blinken/power-rail-probe/doc/1.jpg

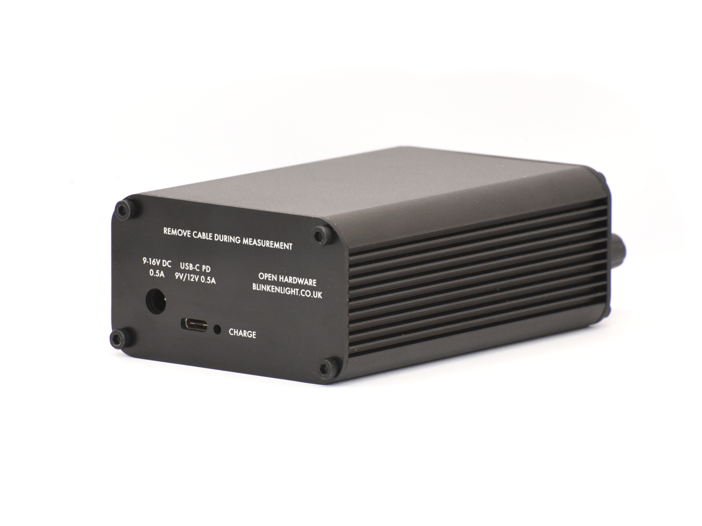
doc/1.jpg
