blinken/power-rail-probe/doc/2.jpg

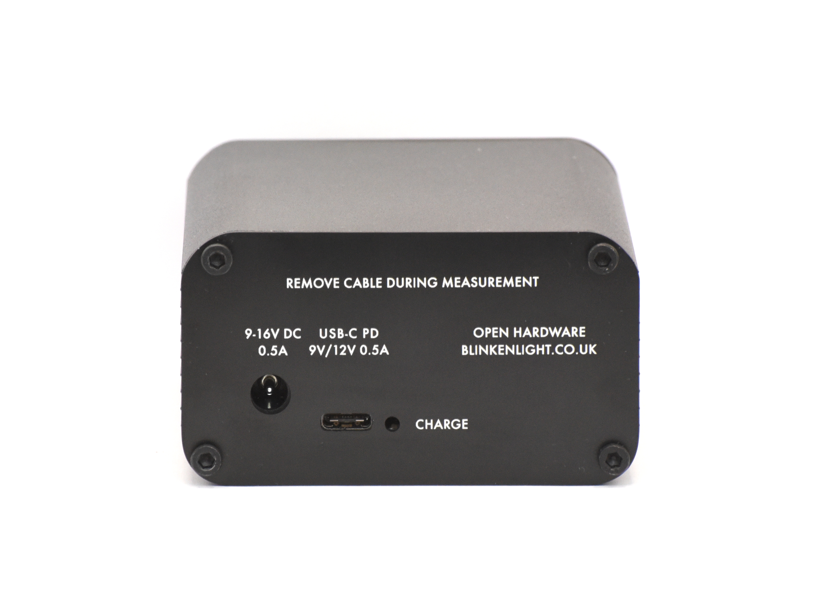
doc/2.jpg
