blinken/power-rail-probe/doc/3.jpg

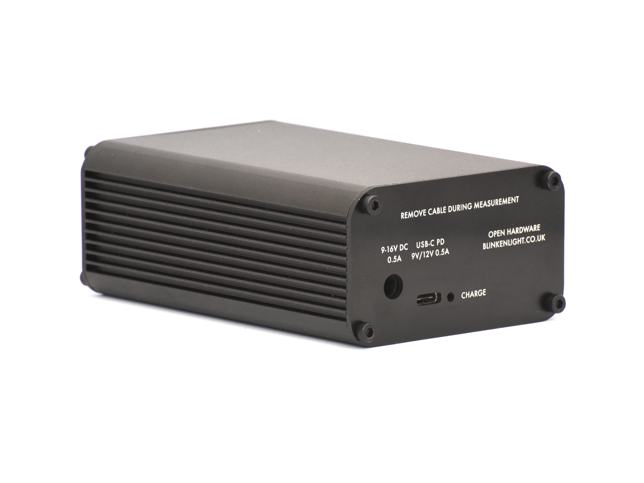
doc/3.jpg
