blinken/power-rail-probe/doc/4-crop.jpg

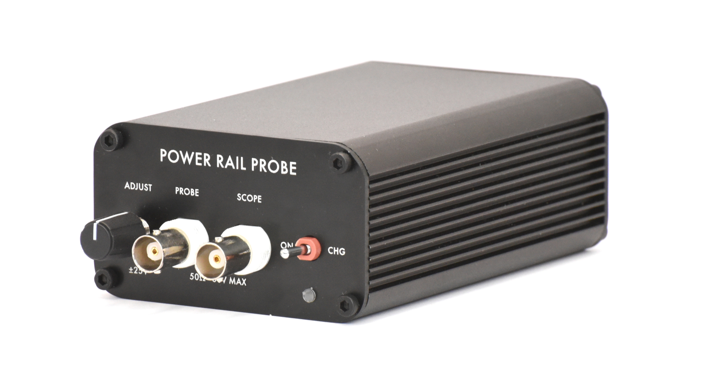
doc/4-crop.jpg
