blinken/power-rail-probe/doc/4.jpg

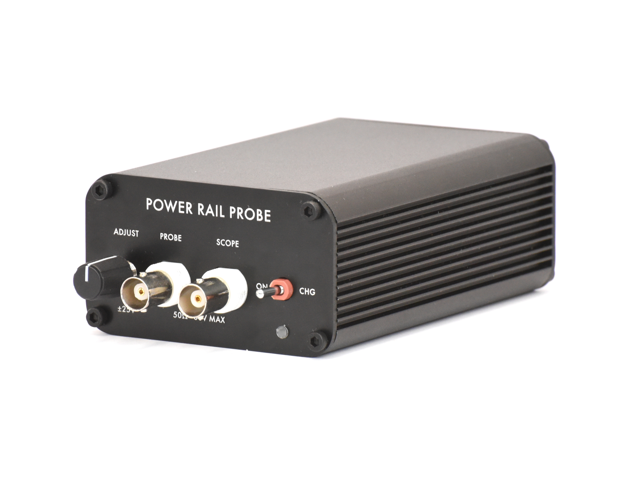
doc/4.jpg
