blinken/power-rail-probe/doc/5.jpg

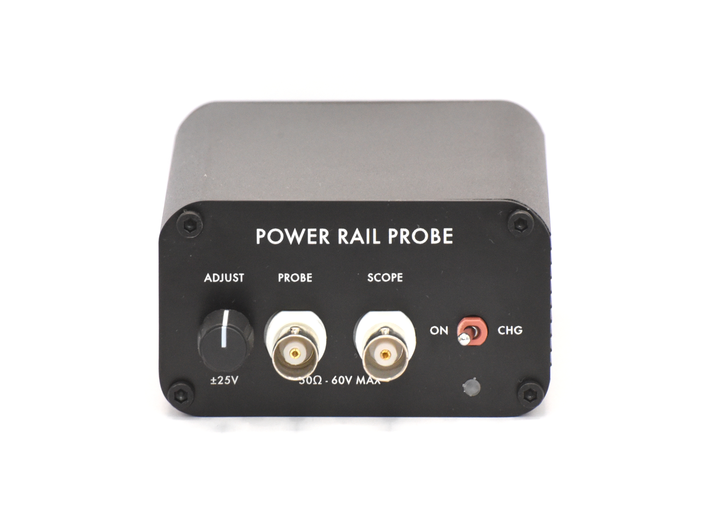
doc/5.jpg
