blinken/power-rail-probe/doc/rear-panel-drawing.png

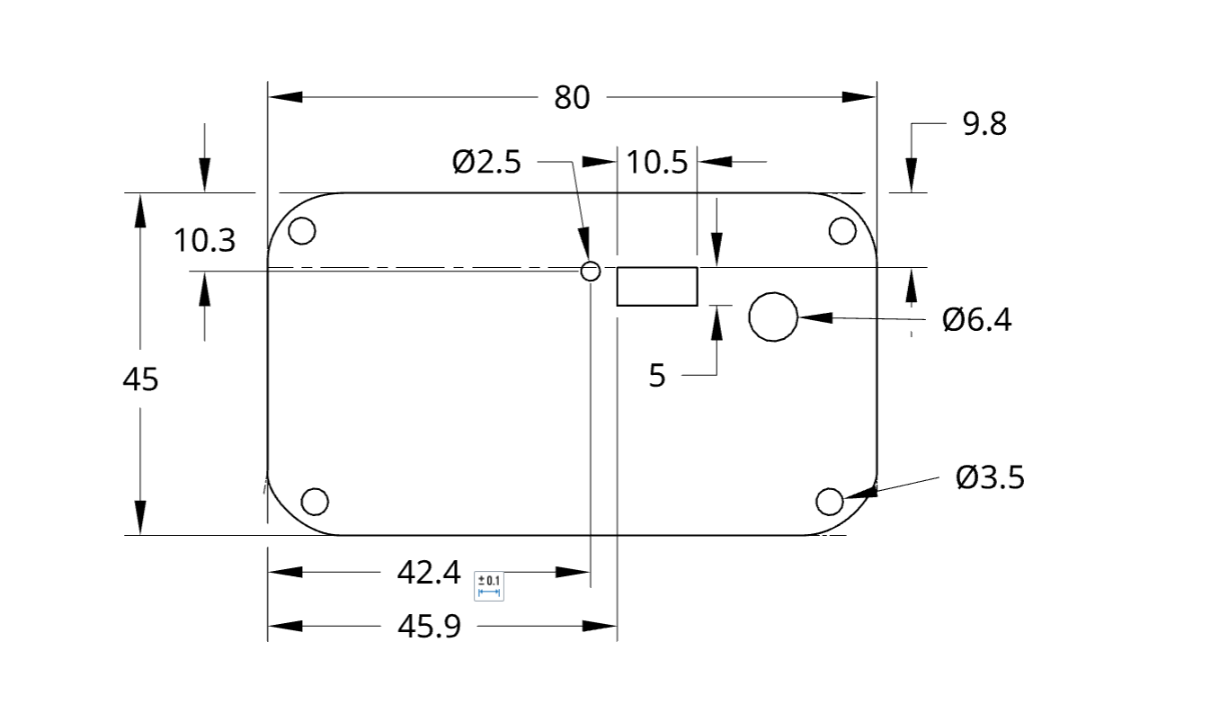
doc/rear-panel-drawing.png
